cunilab/Kivori/firmware/esp32-c3/src/profile.rs

//! Board profiles: the one place concrete panel and pin-map facts are recorded.
//!
//! Two profile classes currently exist:
//!
//! - [`wokwi`] — simulation-only wiring for the Wokwi test environment.
//! - [`physical_st7789`] — hardware-validated ESP32-C3 + ST7789 240x240 profile.
//!
//! Simulation values must never be treated as physical hardware evidence.
//! Physical profile changes require validation against real hardware.

/// The simulation-only profile for `sim/wokwi/diagram-spi.json`.
///
/// Belongs to the Wokwi diagram, not to any board. It is compiled only into simulation artifacts, and
/// `scripts/check-release-surface.sh` proves it is absent from a production firmware library.
#[cfg(any(feature = "wokwi-spi", feature = "wokwi-runtime"))]
pub mod wokwi {
    use crate::display::PanelGeometry;

    /// **Simulation-only** SPI pin profile matching `sim/wokwi/diagram-spi.json`.
    ///
    /// Evidence for the choice, not preference:
    ///
    /// * `wokwi-cli lint` reports the valid pins of `board-esp32-c3-devkitm-1` as
    ///   `0, 1, 2, 3, 4, 5, 6, 7, 8, 9, 10, 18, 19, RST, RX, TX` (plus power/ground). GPIO 11-17 and 20-21
    ///   are not exposed by that part at all.
    /// * `18`/`19` are excluded: they carry USB Serial/JTAG on this SoC, which the runtime itself uses.
    /// * `2`, `8`, `9` are excluded: ESP32-C3 strapping pins.
    ///
    /// These pins belong only to the Wokwi simulation and are unrelated to the
    /// validated physical Kivori ST7789 pin map.
    pub struct WokwiSpiPins;

    impl WokwiSpiPins {
        /// SPI clock (`esp:4` → `lcd:SCK`).
        pub const SCK: u8 = 4;
        /// SPI data out (`esp:5` → `lcd:MOSI`).
        pub const MOSI: u8 = 5;
        /// Chip select (`esp:6` → `lcd:CS`).
        pub const CS: u8 = 6;
        /// Data/command select (`esp:7` → `lcd:D/C`).
        pub const DC: u8 = 7;
        /// Panel reset (`esp:10` → `lcd:RST`).
        pub const RST: u8 = 10;
    }

    /// Geometry of the simulated panel: the full 240x240 window at offset `(0, 0)`.
    ///
    /// `(0, 0)` is correct **for the Wokwi part**; it is not a measurement of any physical module, and must
    /// not be copied into a hardware profile.
    #[must_use]
    pub const fn geometry() -> PanelGeometry {
        PanelGeometry::new(240, 240, 0, 0)
    }
}

/// Verified physical ESP32-C3 + ST7789 240x240 hardware profile.
///
/// Gated on `host-sim` as well as `physical-st7789` so the plain pin-map data (and the
/// profile-collision test in `tests/rotary_input.rs`) is host-testable. The esp-hal-typed
/// helpers below (which cannot build for a host target at all) stay gated on
/// `physical-st7789` alone.
#[cfg(any(feature = "physical-st7789", feature = "host-sim"))]
pub mod physical_st7789 {
    use crate::display::PanelGeometry;
    #[cfg(feature = "physical-st7789")]
    use esp_hal::{gpio::Level, spi::Mode};
    use mipidsi::{
        models::ST7789,
        options::{ColorInversion, ColorOrder, Orientation, Rotation},
    };

    /// SPI clock pin.
    pub const SCK: u8 = 6;

    /// SPI MOSI pin.
    pub const MOSI: u8 = 7;

    /// Display data/command pin.
    pub const DC: u8 = 2;

    /// Display reset pin.
    pub const RST: u8 = 3;

    /// Display backlight pin.
    pub const BL: u8 = 8;

    /// This physical panel does not use chip select.
    pub const CS: Option<u8> = None;

    /// Verified SPI clock. The next throughput lever once frame time is measured on hardware
    /// (needs a signal-integrity check; a full frame is 46 ms of wire time at 20 MHz).
    pub const SPI_CLOCK_HZ: u32 = 20_000_000;

    /// Visible panel width.
    pub const WIDTH: u16 = 240;

    /// Visible panel height.
    pub const HEIGHT: u16 = 240;

    /// Verified visible-area X offset.
    pub const OFFSET_X: u16 = 0;

    /// Verified visible-area Y offset.
    pub const OFFSET_Y: u16 = 0;

    /// Backlight is enabled by driving the pin high.
    pub const BACKLIGHT_ACTIVE_HIGH: bool = true;

    /// Verified physical display geometry.
    #[must_use]
    pub const fn geometry() -> PanelGeometry {
        PanelGeometry::new(WIDTH, HEIGHT, OFFSET_X, OFFSET_Y)
    }

    /// Verified SPI mode.
    #[cfg(feature = "physical-st7789")]
    #[must_use]
    pub const fn spi_mode() -> Mode {
        Mode::_3
    }

    /// Verified physical panel controller.
    #[must_use]
    pub const fn panel_model() -> ST7789 {
        ST7789
    }

    /// Verified panel orientation.
    #[must_use]
    pub fn orientation() -> Orientation {
        Orientation::new().rotate(Rotation::Deg90)
    }

    /// Verified panel color order.
    #[must_use]
    pub const fn color_order() -> ColorOrder {
        ColorOrder::Rgb
    }

    /// Verified panel color inversion.
    #[must_use]
    pub const fn color_inversion() -> ColorInversion {
        ColorInversion::Inverted
    }

    /// Backlight output level.
    #[cfg(feature = "physical-st7789")]
    #[must_use]
    pub const fn backlight_level() -> Level {
        if BACKLIGHT_ACTIVE_HIGH {
            Level::High
        } else {
            Level::Low
        }
    }

    /// HW-040 rotary encoder pin map.
    ///
    /// ISOLATED HERE ON PURPOSE: this is the single place to correct if the wiring changes.
    /// `sw` is sampled by the adapter and consumed by the push-switch gesture machine
    /// (`input::gesture`).
    ///
    /// **This is a SPECIFICATION, not measured evidence.** Unlike the rest of this module
    /// (`SCK`/`MOSI`/`DC`/`RST`/`BL`, all verified against a real board), nobody has verified
    /// continuity of this rotary wiring on physical hardware yet — the maintainer is wiring the
    /// HW-040 module to these GPIOs, and `docs/validation.md` row 3.15 carries the verification. Do not read this
    /// struct as confirmed hardware fact.
    ///
    /// Pin choices, decided deliberately:
    ///
    /// * **CLK = GPIO4, DT = GPIO5, SW = GPIO10.**
    /// * **GPIO9 was rejected for `sw`** despite being the devkit BOOT button. Holding GPIO9 low
    ///   at reset enters ROM download mode, and the encoder switch is Kivori's recovery control —
    ///   a user power-cycling while holding it for recovery would land in the downloader instead
    ///   of booting Kivori.
    /// * GPIO2 and GPIO8 are strapping pins and already taken (D/C, backlight). GPIO0, GPIO1 and
    ///   GPIO20 carry the contextual buttons (see [`CONTEXT_BUTTONS`]); GPIO21 stays free as the
    ///   UART0 TX boot / log console.
    /// * **Known tradeoff:** only GPIO0-5 can wake the C3 from deep sleep, so `sw` on GPIO10
    ///   cannot. Kivori's Display Sleep is panel blanking with the MCU awake, so this is outside
    ///   the MVP contract; if deep-sleep wake is ever wanted, `sw` moves to GPIO1.
    ///
    /// The three lines are wired active-low (HW-040 COM to GND) and read with internal pull-ups;
    /// the adapter in `physical_rotary` inverts them to logical levels.
    #[derive(Debug, Clone, Copy)]
    pub struct RotaryProfile {
        /// Quadrature channel A (CLK) pin.
        pub clk: u8,
        /// Quadrature channel B (DT) pin.
        pub dt: u8,
        /// Push-switch (SW) pin.
        pub sw: u8,
    }

    /// HW-040 wiring specification decided for this board (see [`RotaryProfile`]).
    pub const ROTARY: RotaryProfile = RotaryProfile {
        clk: 4,
        dt: 5,
        sw: 10,
    };

    /// The three contextual buttons, left to right. Each is a plain momentary switch from the
    /// GPIO to GND, read active-low with the internal pull-up; no external parts.
    ///
    /// These are the only free GPIOs left, decided deliberately:
    ///
    /// * **GPIO0 and GPIO1** are the XTAL_32K pair. They are plain GPIOs only when no 32.768 kHz
    ///   crystal is fitted: check the devkit first (validation row 5.1).
    /// * **GPIO20** is UART0 RX. Kivori never reads UART0 (the data link is USB Serial/JTAG and
    ///   `esp-println` only writes TX), so the boot log on GPIO21 keeps working.
    /// * **GPIO9 stays unused**: pressed at reset it would enter ROM download mode.
    /// * None of the three is a strapping pin, so a button held at power-on cannot change how the
    ///   chip boots.
    ///
    /// Like the encoder map, a specification until physically verified.
    pub const CONTEXT_BUTTONS: [u8; 3] = [0, 1, 20];
}
