cunilab/Kivori/firmware/esp32-c3/tests/render_parity.rs

//! Render-parity test (T069; SC-005): the firmware's change-driven, tile-by-tile render path
//! produces exactly the same pixels as a single full-frame render of the shared renderer. This is
//! what lets the host golden frames stand in for the on-device image.
#![cfg(feature = "host-sim")]

use kivori_asset_compiler::compile_default_blob;
use kivori_assets::AssetBlob;
use kivori_firmware::render::{TileRenderer, TILE_COUNT};
use kivori_firmware::sim::{CaptureDisplay, FRAME_PIXELS};
use kivori_framebuffer::{hash_rgb565, TileBand};
use kivori_model::{CompanionState, Rect, Rgb565};
use kivori_renderer::render_scene;

#[test]
fn buffered_frames_clear_old_pixels_and_retry_a_failed_transfer() {
    use kivori_firmware::ports::DisplaySink;
    use kivori_model::MascotAnimator;

    struct FailOnce {
        display: Box<CaptureDisplay>,
        remaining: Option<usize>,
    }
    impl FailOnce {
        /// A window either transfers whole or fails before any pixel moves.
        fn fail_or_count(&mut self) -> Result<(), ()> {
            if let Some(remaining) = &mut self.remaining {
                if *remaining == 0 {
                    self.remaining = None;
                    return Err(());
                }
                *remaining -= 1;
            }
            Ok(())
        }
    }
    impl DisplaySink for FailOnce {
        type Error = ();
        fn blit_tile(&mut self, rect: Rect, pixels: &[Rgb565]) -> Result<(), ()> {
            self.fail_or_count()?;
            self.display.blit_tile(rect, pixels).unwrap();
            Ok(())
        }
        fn blit_tiles(&mut self, rect: Rect, tiles: &[Rgb565], cols: u16) -> Result<(), ()> {
            self.fail_or_count()?;
            self.display.blit_tiles(rect, tiles, cols).unwrap();
            Ok(())
        }
    }

    let bytes = compile_default_blob();
    let blob = AssetBlob::parse(&bytes).unwrap();
    let mut storage: Box<[Rgb565; FRAME_PIXELS]> = vec![Rgb565::from_raw(0); FRAME_PIXELS]
        .into_boxed_slice()
        .try_into()
        .unwrap();
    let mut renderer = TileRenderer::with_frame_buffer(&mut storage);
    let mut sink = FailOnce {
        display: Box::new(CaptureDisplay::new()),
        remaining: Some(1), // the first band (two tile rows) lands, the second fails
    };
    let mut animator = MascotAnimator::new(CompanionState::Happy, 0);
    let pose = animator.pose_at(200);
    assert!(renderer
        .render_animation(&blob, animator.target(), &pose, &mut sink)
        .is_err());
    renderer
        .render_animation(&blob, animator.target(), &pose, &mut sink)
        .unwrap();
    assert_eq!(
        sink.display.blits as usize, TILE_COUNT,
        "only successful transfers enter the cache"
    );
    for ms in [200, 400, 700, 1200, 1600, 3600] {
        if ms == 700 {
            animator.set_state(CompanionState::Idle, ms);
        }
        let pose = animator.pose_at(ms);
        let mut expected = vec![Rgb565::from_raw(0); FRAME_PIXELS];
        let mut band = TileBand::new(Rect::new(0, 0, 240, 240), &mut expected).unwrap();
        kivori_renderer::render_pose(
            &blob,
            blob.scene(animator.target()).unwrap(),
            &pose,
            &mut band,
        )
        .unwrap();
        renderer
            .render_animation(&blob, animator.target(), &pose, &mut sink)
            .unwrap();
        assert_eq!(sink.display.frame(), expected, "prepared pose at {ms} ms");
    }
    let before = sink.display.blits;
    renderer
        .render_animation(&blob, animator.target(), &animator.pose_at(3600), &mut sink)
        .unwrap();
    assert_eq!(
        sink.display.blits, before,
        "identical buffered frame sends nothing"
    );
    renderer.invalidate();
    renderer
        .render_animation(&blob, animator.target(), &animator.pose_at(3600), &mut sink)
        .unwrap();
    assert_eq!((sink.display.blits - before) as usize, TILE_COUNT);
}
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
